keppler/co2/beep.c

/*         ___    ___
 *  __ ___|_  )__/ __| ___ _ _  ___ ___ _ _
 * / _/ _ \/ /___\__ \/ -_) ' \(_-</ _ \ '_|
 *_\__\___/___|  |___/\___|_||_/__/\___/_|_________________________________
 * CO₂ Sensor for Caving -- https://github.com/keppler/co2
 * Driver for sound transducer
 */

#include <stdint.h>
#include <avr/pgmspace.h>
#include <util/delay.h>
#include "beep.h"

uint8_t beep_volume = 3;

static const uint8_t melody[] PROGMEM = {
    6, 8, 12, 16, 30, 44,  /* index to melodies */
    250, 10,               /* short */
    220, 30, 250, 15,      /* relax */
    250, 15, 220, 30,      /* warn */
    250, 20, 220, 14, 190, 14, 0, 6, 250, 6, 0, 6, 250, 6,   /* startup */
    190, 20, 220, 14, 250, 14, 0, 6, 250, 6, 0, 6, 250, 6    /* shutdown */
};

void beep_init(void) {
    /* PB4: PWM with OC1B pin (PB4) */
    DDRB |= (1 << DDB4);
    PORTB &= ~(1 << PB4);
}

void beep(const beep_t t) {
    if (beep_volume == 0) return;

    uint8_t len;
    TCCR1 = 1<<CS10;
    GTCCR = 1 << PWM1B | 1 << COM1B1;

    uint8_t pos;
    for (pos=pgm_read_byte(melody + t); pos < pgm_read_byte(melody + t + 1); pos+=2) {
        uint8_t tmp = pgm_read_byte(melody + pos);
        OCR1C = tmp;
        OCR1B = tmp >> beep_volume;
        for (len=pgm_read_byte(melody + pos + 1); len>0; len-=1) _delay_ms(10);
    }

    TCCR1 = 0;
    GTCCR = 0;
}
